DCentralTech/bitaxe104/3d/21-0164B_L622-1_MXM.step

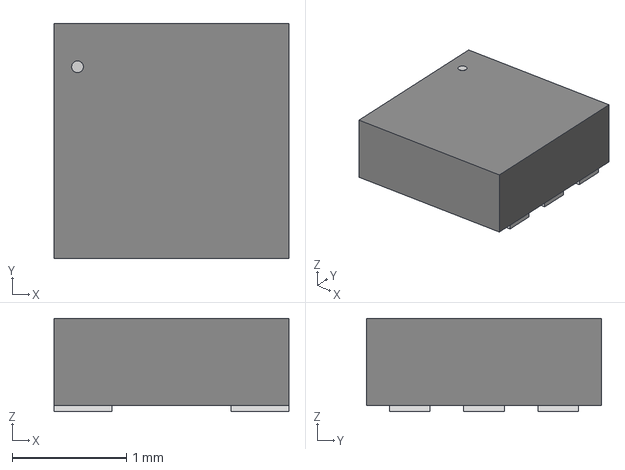
[picture p26: CAD file, 2024-08-15]
3d/21-0164B_L622-1_MXM.step
2.06 x 2.06 x 0.815 mm
