DCentralTech/bitaxe104/3d/DQG0008A.stp

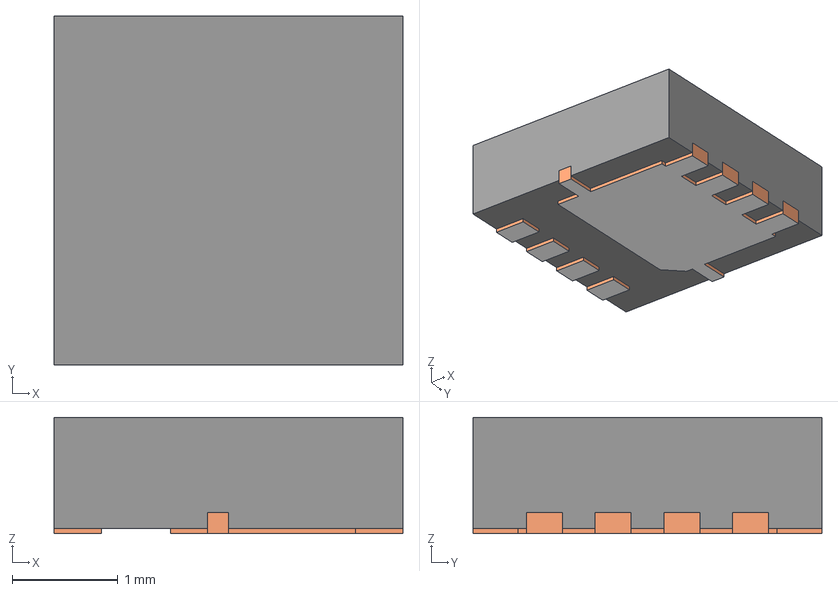
[picture p28: CAD file, 2024-08-15]
3d/DQG0008A.stp
3.30 x 3.30 x 1.10 mm
BODY-SON
FRAME-DQG0008A
PIN1-ID
