DCentralTech/bitaxe104/3d/XRCGB27M120F3M10R0_MUR.step

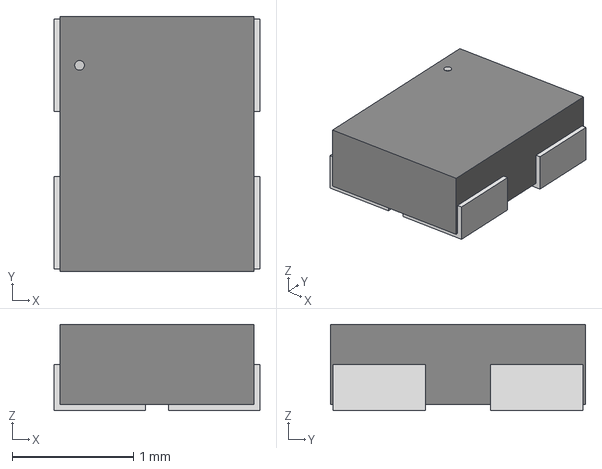
[picture p30: CAD file, 2024-08-15]
3d/XRCGB27M120F3M10R0_MUR.step
1.70 x 2.11 x 0.714 mm
